MichielVanwelsenaere/HomeAutomation.ModbusRtuSensorHub/docs/Example-projects/Blink/Blink.ino

// the setup function runs once when you press reset or power the board
void setup() {
  // initialize digital pin LED_BUILTIN as an output.
  pinMode(10, OUTPUT);
}

// the loop function runs over and over again forever
void loop() {
  digitalWrite(10, HIGH);   // turn the LED on (HIGH is the voltage level)
  delay(1000);                       // wait for a second
  digitalWrite(10, LOW);    // turn the LED off by making the voltage LOW
  delay(1000);                       // wait for a second
}
